DIGITALatCalPolyPomonaCPP/SIDEKICK-Prev.-TheSmartphoneProject-/subsystems/haptics/source/README.md

- What us a haptic motor driver?
    A **haptic motor driver** is an integrated circuit (IC) that controls **vibration motors** to produce **tactile feedback** —
    the kind of feedback you feel as a buzz, tap, pulse, or click when using a smartphone, game controller, smartwatch, or touchscreen.
